jaylogue/pdp-1105-console-usb-adapter/schematic/pdp-1105-console-usb-adapter.kicad_sch

## KiCad design schematic/pdp-1105-console-usb-adapter.kicad_sch (2023-11-19)

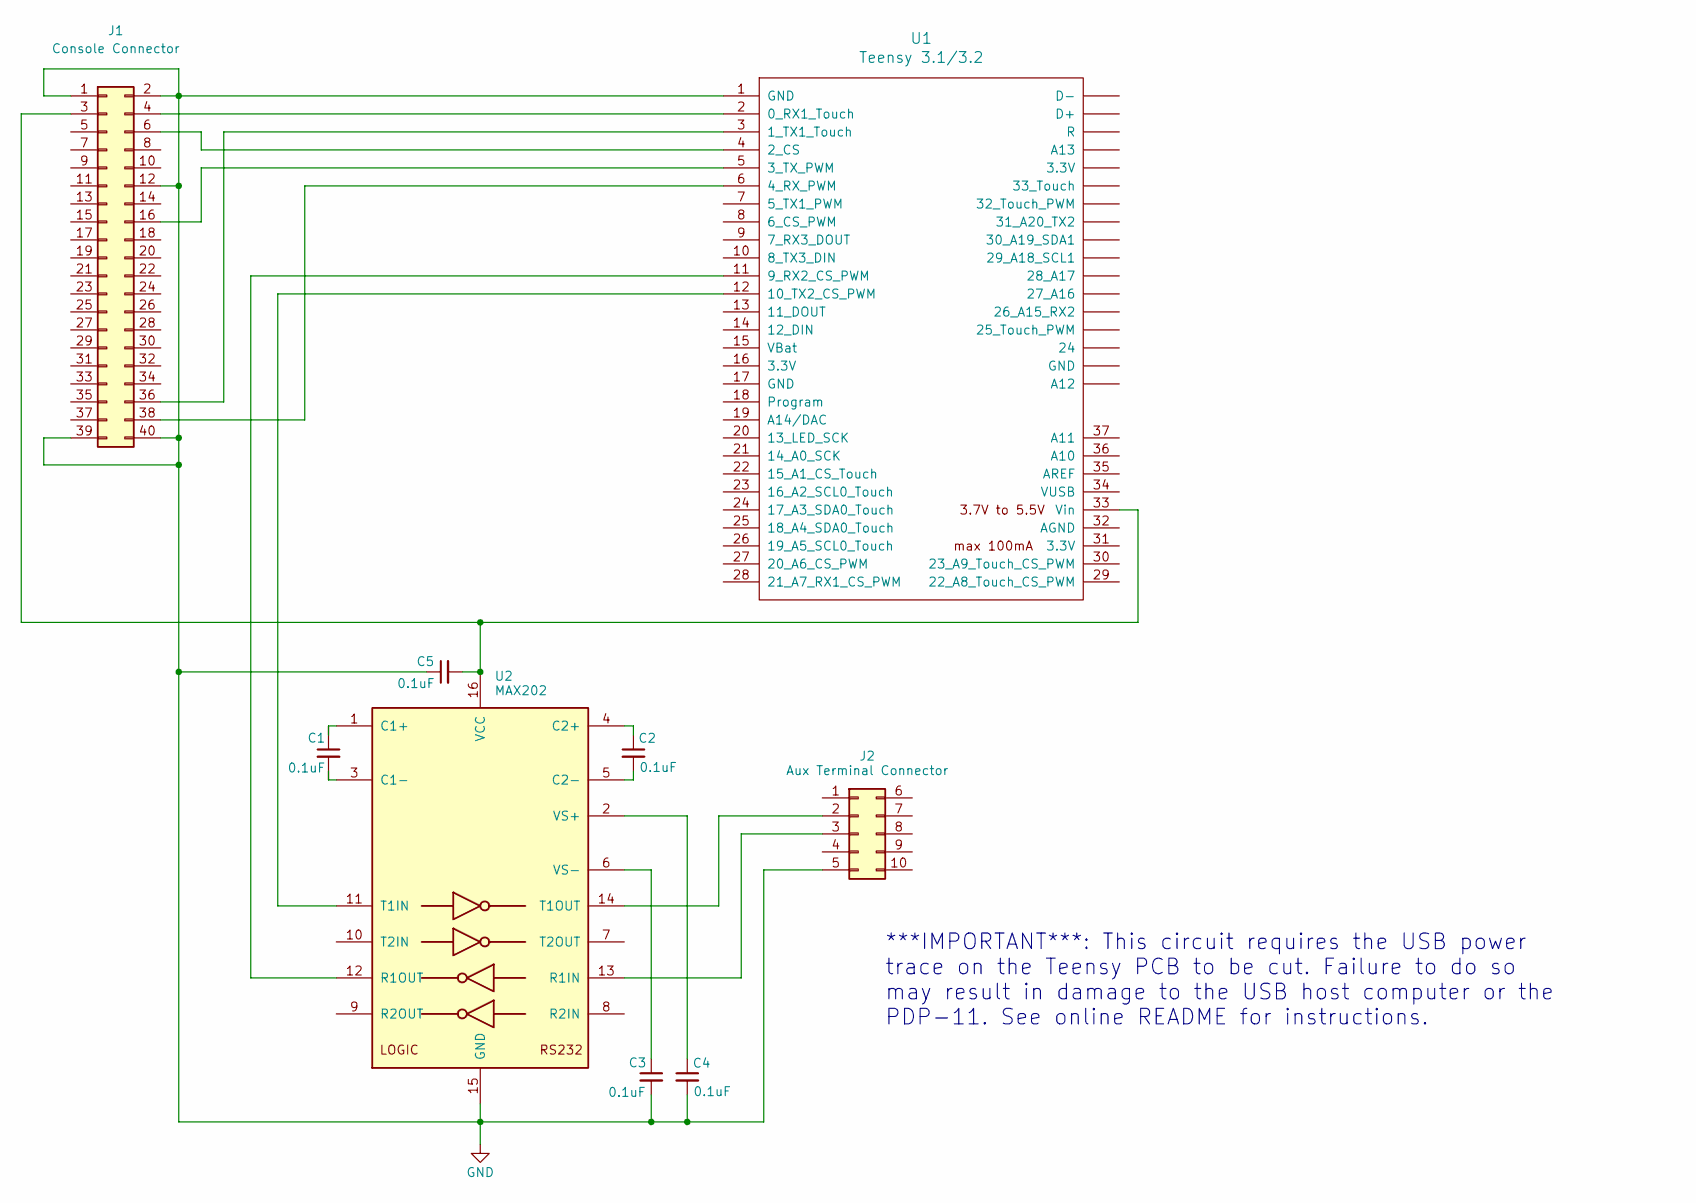
[picture p13: schematic pdp-1105-console-usb-adapter.kicad_sch]

Parts:
C1, C2, C3, C4, C5: 0.1uF; C_0805_2012Metric_Pad1.18x1.45mm_HandSolder
J1: Console Connector; IDC-Header_2x20_P2.54mm_Vertical
J2: Aux Terminal Connector; IDC-Header_2x05_P2.54mm_Vertical
U1: Teensy 3.1/3.2; Teensy30_31_32_LC
U2: MAX202; DIP-16_W7.62mm

Connections:
GND: C3.2, C4.2, C5.1, J1.1, J1.2, J1.12, J1.39, J1.40, J2.5, U1.1 (GND), U2.15 (GND)
unnamed: C1.1, U2.1 (C1+)
unnamed: C1.2, U2.3 (C1-)
unnamed: C2.1, U2.4 (C2+)
unnamed: C2.2, U2.5 (C2-)
unnamed: C3.1, U2.6 (VS-)
unnamed: C4.1, U2.2 (VS+)
unnamed: C5.2, J1.3, U1.33 (Vin), U2.16 (VCC)
unnamed: J1.4, U1.2 (0_RX1_Touch)
unnamed: J1.6, U1.4 (2_CS)
unnamed: J1.16, U1.5 (3_TX_PWM)
unnamed: J1.36, U1.3 (1_TX1_Touch)
unnamed: J1.38, U1.6 (4_RX_PWM)
unnamed: J2.2, U2.14 (T1OUT)
unnamed: J2.3, U2.13 (R1IN)
unnamed: U1.11 (9_RX2_CS_PWM), U2.12 (R1OUT)
unnamed: U1.12 (10_TX2_CS_PWM), U2.11 (T1IN)

Notes on the sheet:
***IMPORTANT***: This circuit requires the USB power trace on the Teensy PCB to be cut. Failure to do so may result in damage to the USB host computer or the PDP-11. See online README for instructions.
